Sebski123/p-ktane/Design/Photos/20190628_165110.jpg

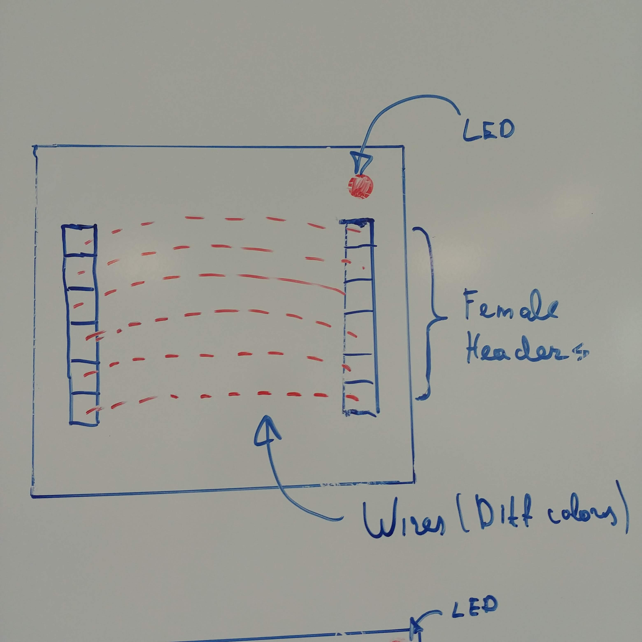
Design/Photos/20190628_165110.jpg
