Sebski123/p-ktane/Design/Photos/20190628_165116.jpg

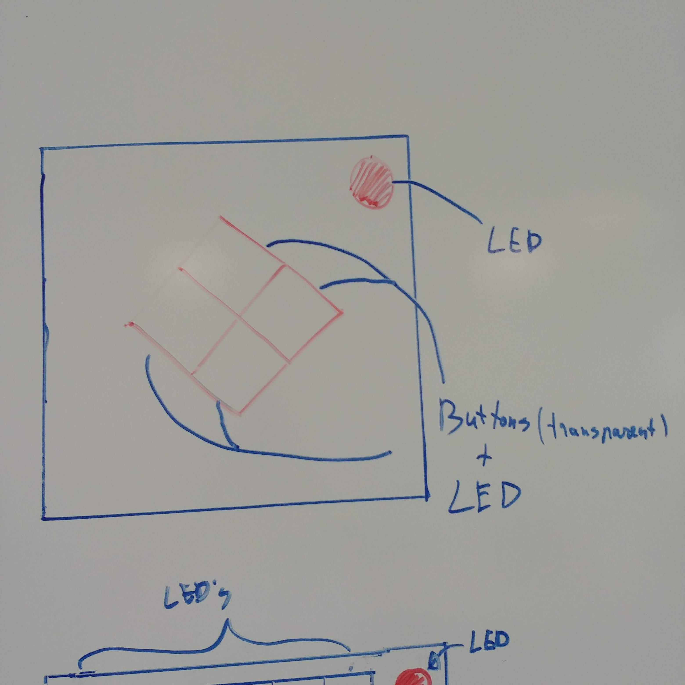
Design/Photos/20190628_165116.jpg
