Sebski123/p-ktane/Design/Photos/20190628_165210.jpg

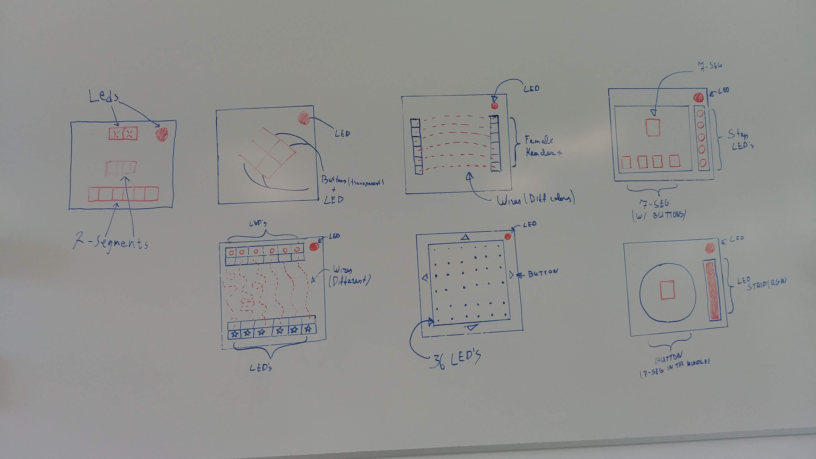
Design/Photos/20190628_165210.jpg
