Sebski123/p-ktane/Modules/buttonModule/MXFrameBottom.SLDPRT

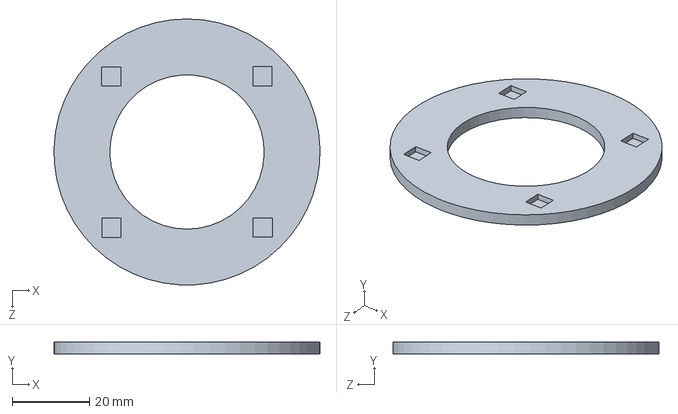
[picture p24: CAD file, 2020-05-21]
Modules/buttonModule/MXFrameBottom.SLDPRT
69.0 x 3.00 x 69.0 mm
