Sebski123/p-ktane/Modules/mazeModule/Maze face plate.SLDPRT

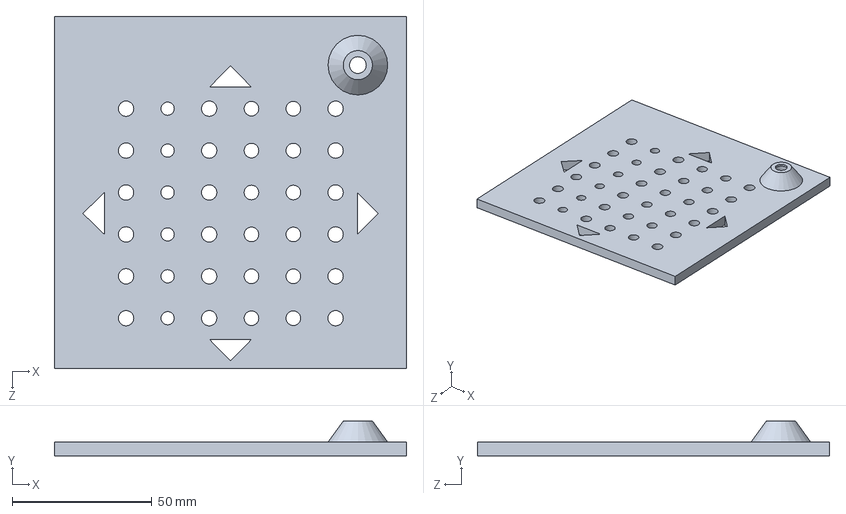
[picture p25: CAD file, 2020-05-14]
Modules/mazeModule/Maze face plate.SLDPRT
126.0 x 12.5 x 126.0 mm
