Sebski123/p-ktane/Modules/memoryModule/TRIANGLE.SLDPRT

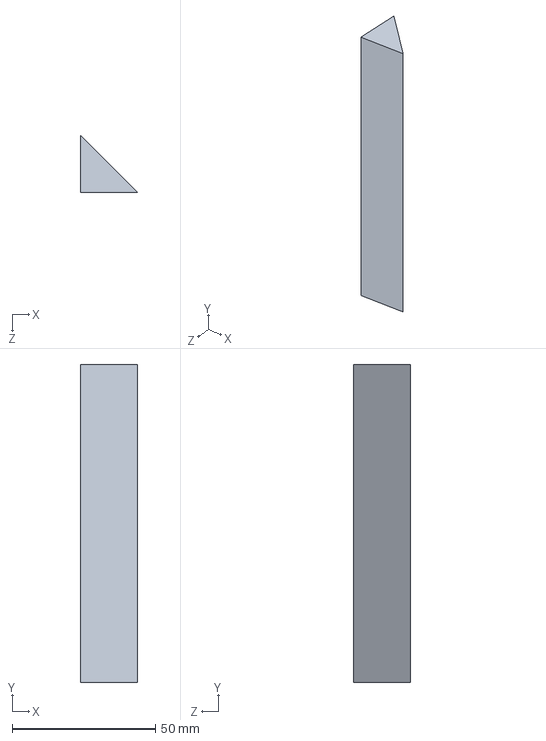
[picture p26: CAD file, 2020-05-26]
Modules/memoryModule/TRIANGLE.SLDPRT
20.0 x 111.0 x 20.0 mm
