Sebski123/p-ktane/Modules/simonSaysModule/front_plate_simon.stp

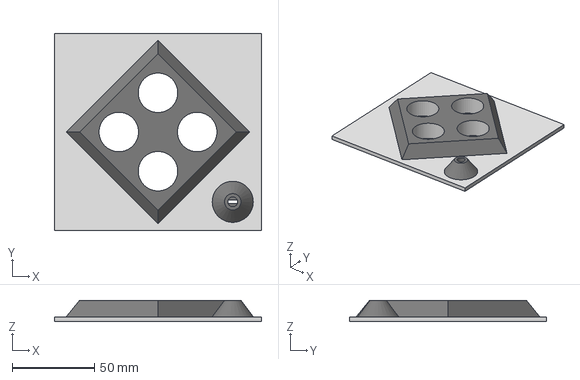
[picture p27: CAD file, 2020-04-02]
Modules/simonSaysModule/front_plate_simon.stp
126.0 x 120.0 x 13.0 mm
