Sebski123/p-ktane/Design/Box/Box parts/BoxTop.SLDPRT

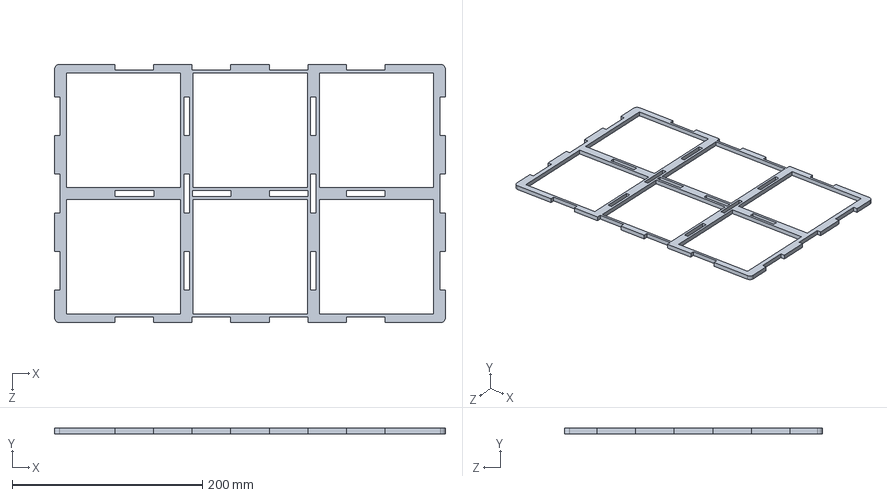
[picture p28: CAD file, 2020-04-29]
Design/Box/Box parts/BoxTop.SLDPRT
410.7 x 6.00 x 271.4 mm
