Sebski123/p-ktane/Design/Box/DXF FILES/SidesSmall.dxf

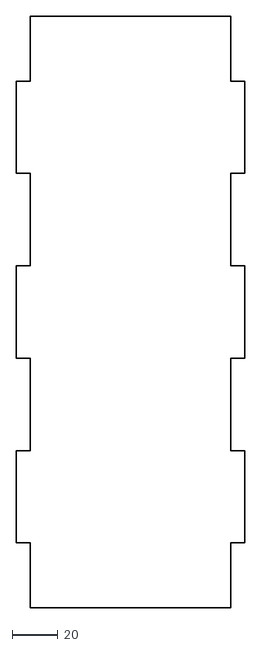
[picture p29: CAD file, 2020-04-29]
Design/Box/DXF FILES/SidesSmall.dxf
100.0 x 259.4
