Sebski123/p-ktane/Modules/buttonModule/MXFrameTop.SLDPRT

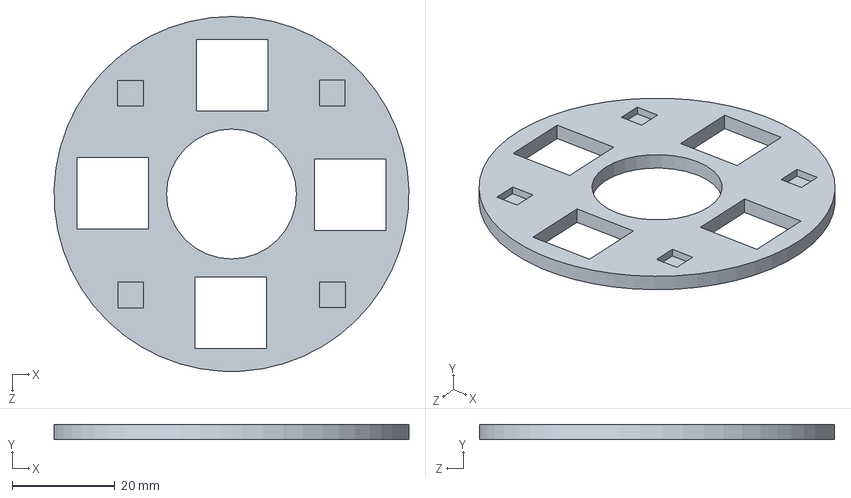
[picture p30: CAD file, 2020-05-21]
Modules/buttonModule/MXFrameTop.SLDPRT
69.0 x 3.00 x 69.0 mm
