Sebski123/p-ktane/Design/Box/Box parts/BoxBottom.SLDPRT

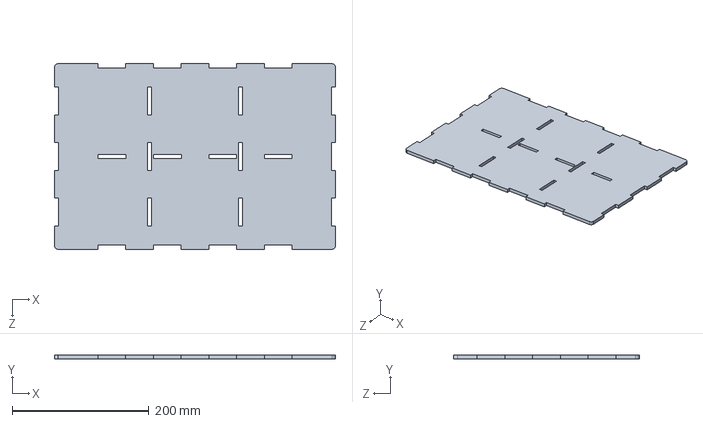
[picture p31: CAD file, 2020-04-29]
Design/Box/Box parts/BoxBottom.SLDPRT
410.7 x 6.00 x 271.4 mm
