Sebski123/p-ktane/Design/Box/DXF FILES/BoxBottom.dxf

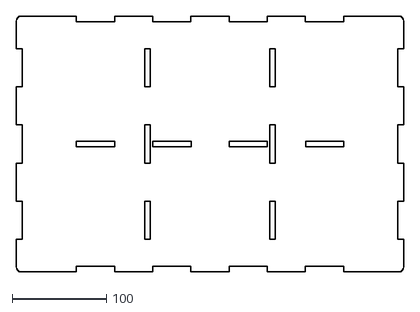
[picture p32: CAD file, 2020-04-29]
Design/Box/DXF FILES/BoxBottom.dxf
410.7 x 271.4
