Sebski123/p-ktane/Modules/buttonModule/Button base.SLDPRT

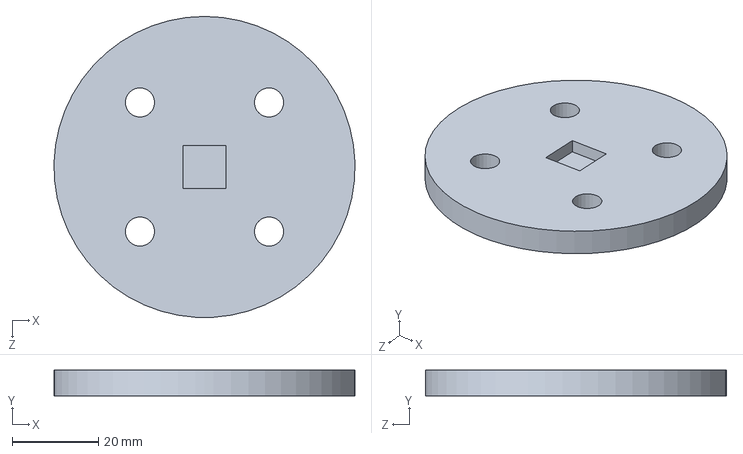
[picture p33: CAD file, 2020-05-21]
Modules/buttonModule/Button base.SLDPRT
70.0 x 6.00 x 70.0 mm
