Sebski123/p-ktane/Modules/memoryModule/Memory button base.SLDPRT

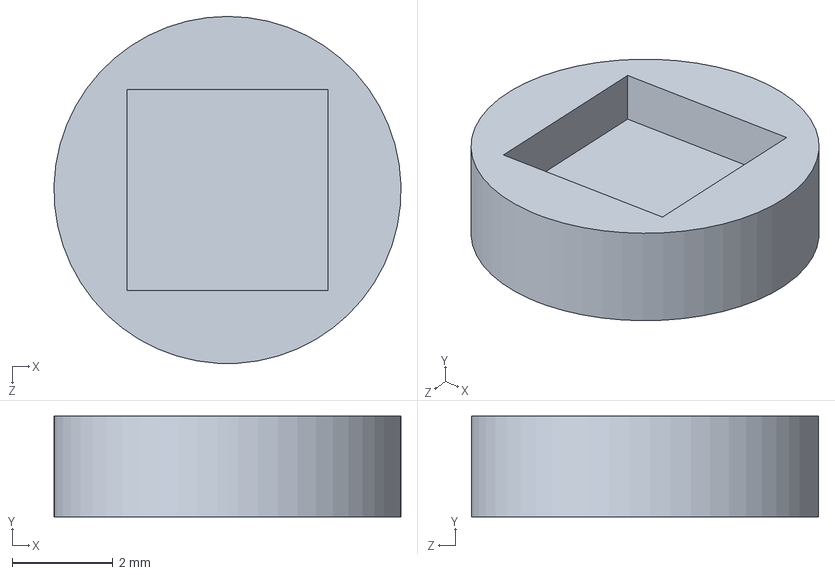
[picture p34: CAD file, 2020-04-14]
Modules/memoryModule/Memory button base.SLDPRT
6.90 x 2.00 x 6.90 mm
