Sebski123/p-ktane/Design/Box/Box parts/InsideLarge.SLDPRT

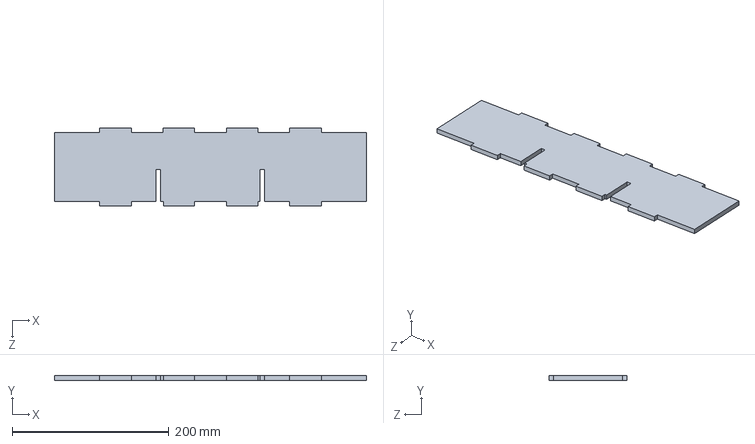
[picture p35: CAD file, 2020-04-29]
Design/Box/Box parts/InsideLarge.SLDPRT
398.7 x 6.00 x 100.0 mm
