Sebski123/p-ktane/Design/Box/DXF FILES/SidesLarge.dxf

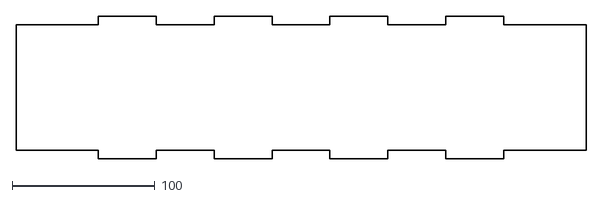
[picture p36: CAD file, 2020-04-29]
Design/Box/DXF FILES/SidesLarge.dxf
398.8 x 100.0
