Sebski123/p-ktane/Modules/buttonModule/MXSwitchLegs.SLDPRT

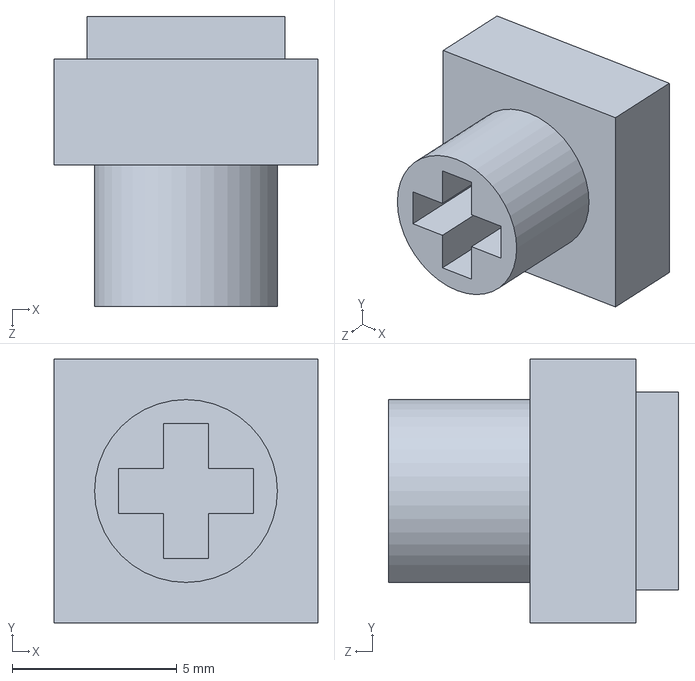
[picture p37: CAD file, 2020-05-21]
Modules/buttonModule/MXSwitchLegs.SLDPRT
8.00 x 8.00 x 8.80 mm
