Sebski123/p-ktane/Modules/memoryModule/front_plate_memory.stp

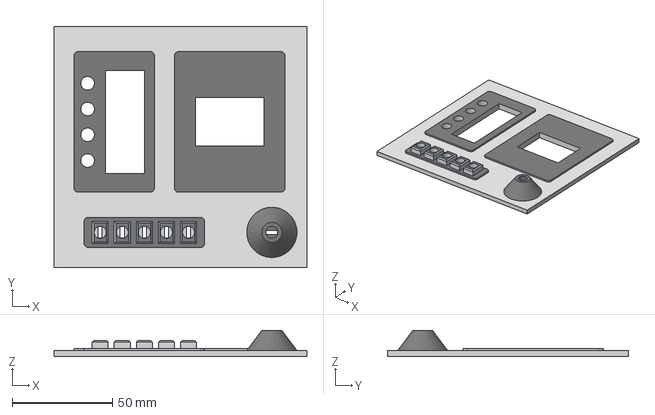
[picture p38: CAD file, 2020-04-02]
Modules/memoryModule/front_plate_memory.stp
126.0 x 120.0 x 13.0 mm
