Sebski123/p-ktane/Design/Box/DXF FILES/InsideSmall.dxf

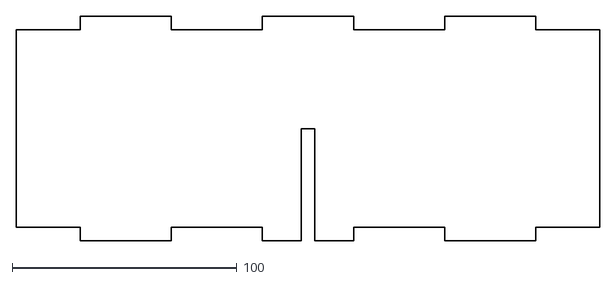
[picture p39: CAD file, 2020-04-29]
Design/Box/DXF FILES/InsideSmall.dxf
259.4 x 100.0
