Sebski123/p-ktane/Modules/buttonModule/Button face plate side bar.SLDPRT

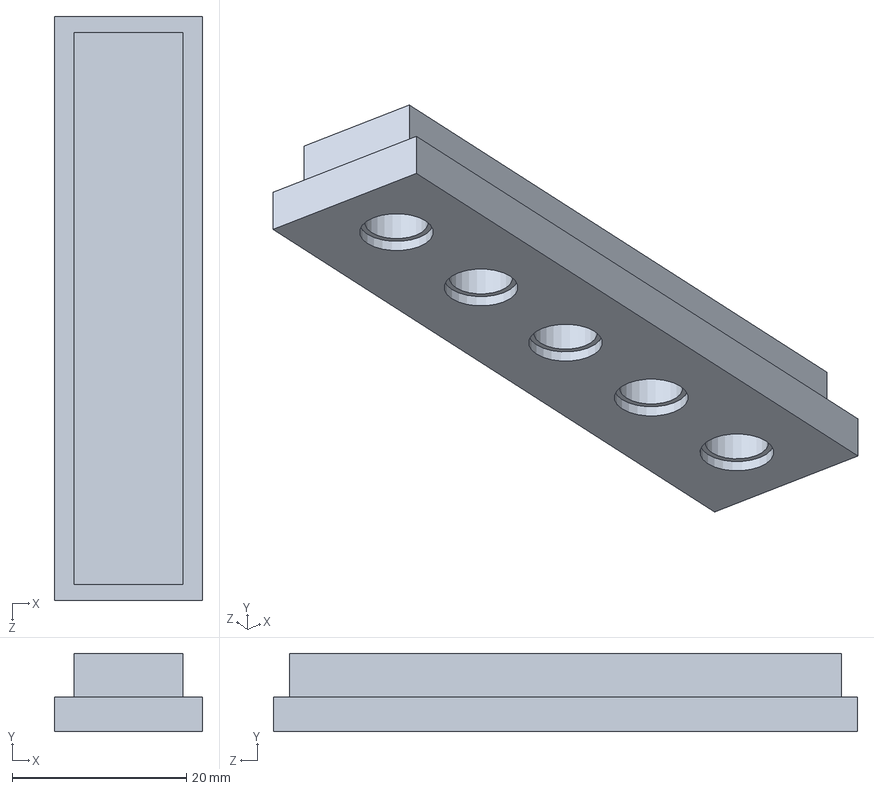
[picture p40: CAD file, 2020-05-05]
Modules/buttonModule/Button face plate side bar.SLDPRT
17.0 x 9.00 x 67.0 mm
