Sebski123/p-ktane/Modules/buttonModule/Button face plate.SLDPRT

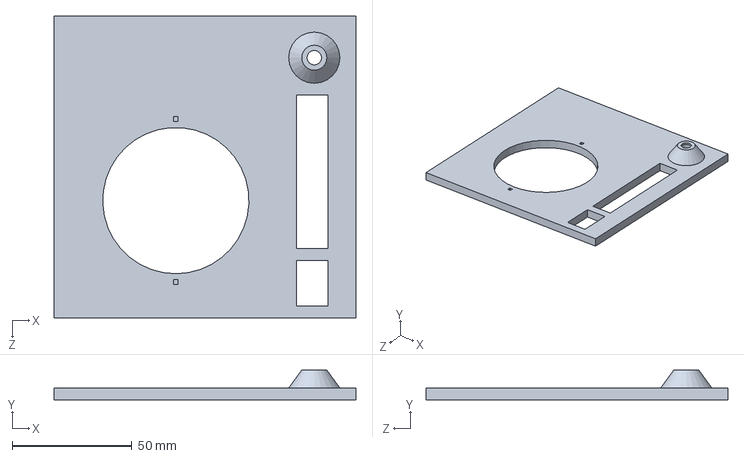
[picture p41: CAD file, 2020-04-22]
Modules/buttonModule/Button face plate.SLDPRT
126.0 x 12.5 x 126.0 mm
