Sebski123/p-ktane/Modules/buttonModule/Button middle.SLDPRT

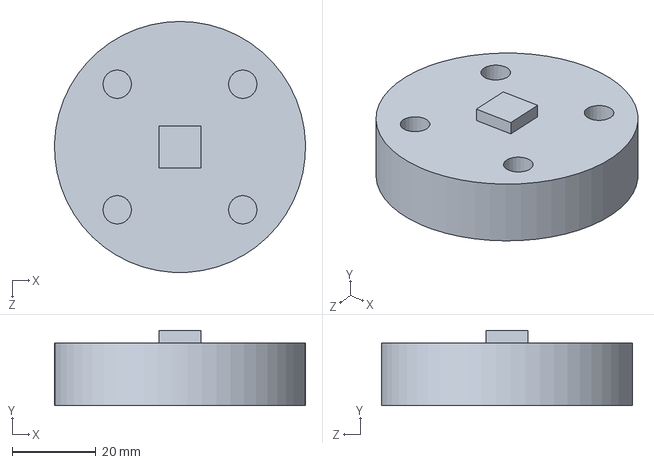
[picture p42: CAD file, 2020-04-22]
Modules/buttonModule/Button middle.SLDPRT
60.0 x 18.0 x 60.0 mm
