Sebski123/p-ktane/Modules/buttonModule/Button face plate ring.SLDPRT

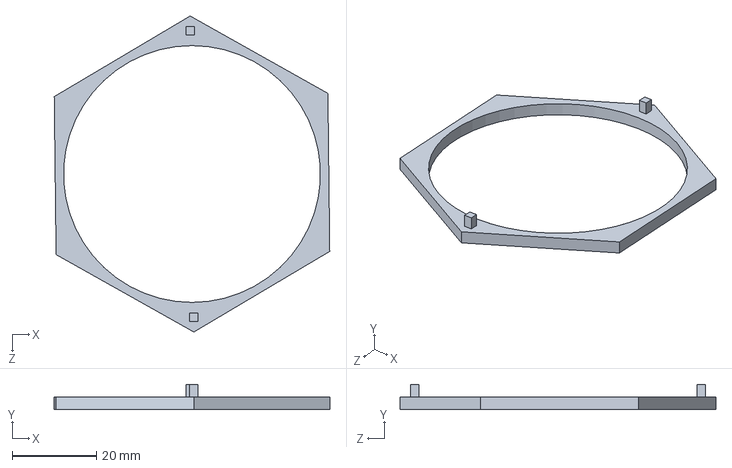
[picture p43: CAD file, 2020-04-14]
Modules/buttonModule/Button face plate ring.SLDPRT
65.4 x 6.00 x 75.1 mm
