Sebski123/p-ktane/Modules/buttonModule/Button top.SLDPRT

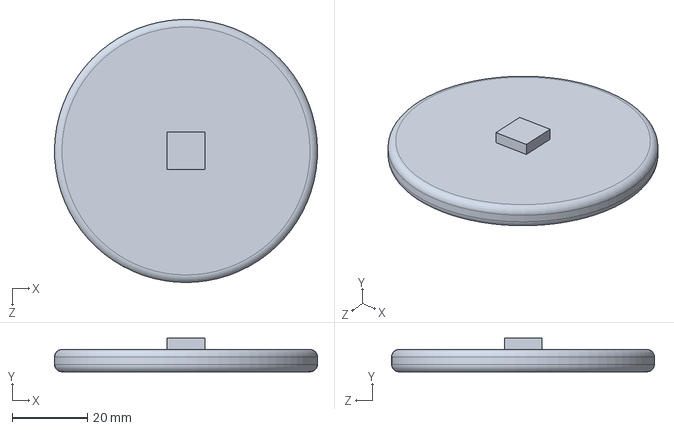
[picture p44: CAD file, 2020-04-10]
Modules/buttonModule/Button top.SLDPRT
70.0 x 9.00 x 70.0 mm
