Sebski123/p-ktane/Design/Schematics/allModules.sch

## EAGLE design Design/Schematics/allModules.sch (2020-06-12)

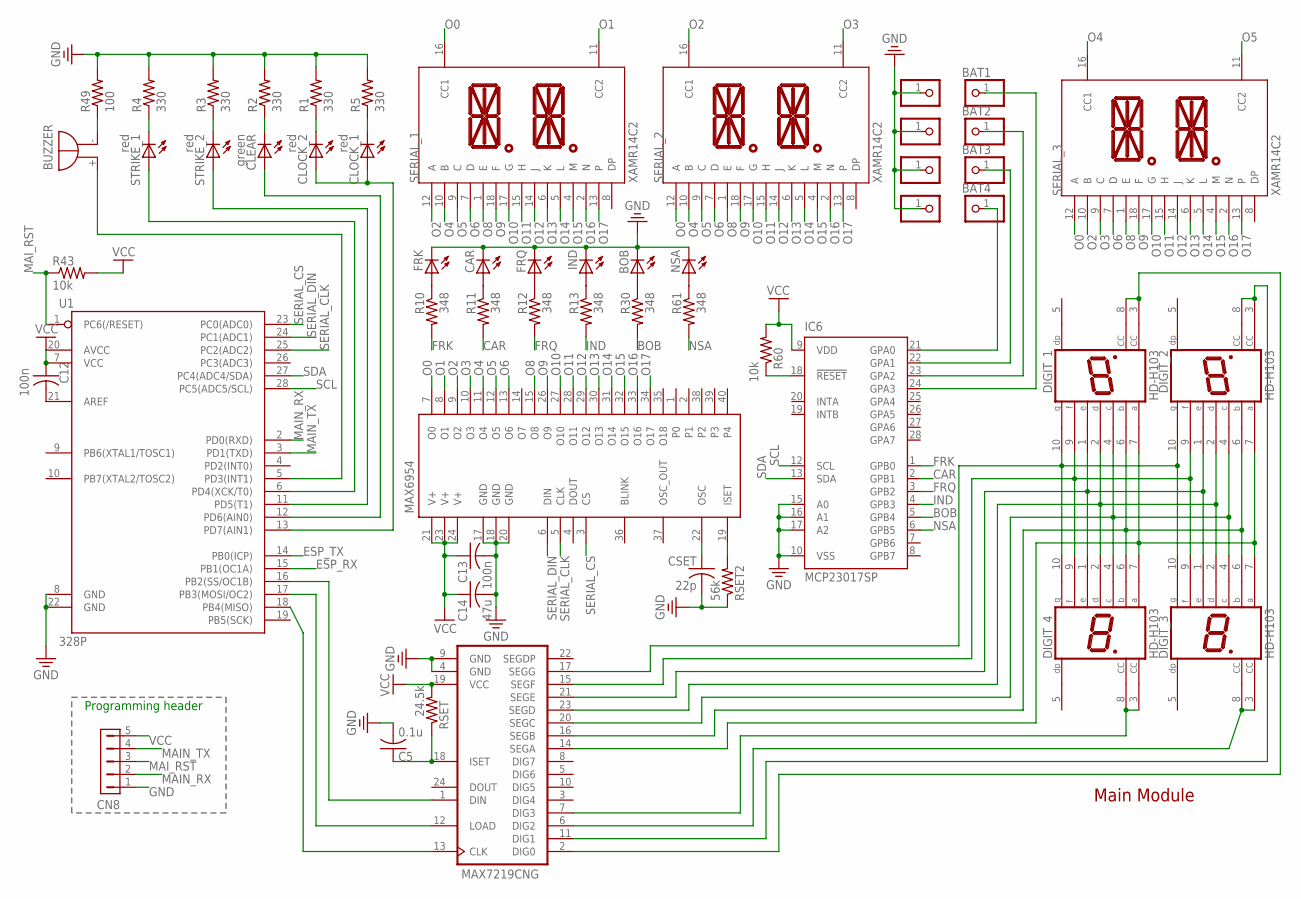
[picture p52: schematic allModules.sch, sheet 1]

Parts:
BAT1, BAT2, BAT3, BAT4: PINHD-1X1; 1X01
BOB: LED5MM
BUZZER: EB2209A
C5: 0.1u; C025-024X044
C12, C13: 100n; C025-024X044
C14: 47u; C025-024X044
CAR: LED5MM
CLEAR: green; LED5MM
CLOCK_1, CLOCK_2: red; LED5MM
CN8: HDR-1X5-SIP-100; SIP-100-5V
CSET: 22p; C025-024X044
DIGIT_1, DIGIT_2, DIGIT_3, DIGIT_4: HD-H103; HDSP-M
FRK: LED5MM
FRQ: LED5MM
IC1: MAX7219CNG; DIL24-3
IC6: MCP23017SP; DIL28-3
IND: LED5MM
JP17, JP18, JP19, JP20: PINHD-1X1; 1X01
MAX6954: MAX6954
NSA: LED5MM
R1, R2, R3, R4, R5: 330; 0309/12
R10, R11, R12, R13, R30, R61: 348; 0204/7
R43: 10k; 0309/12
R49: 100; 0309/12
R60: 10k; 0204/7
RSET: 24.5k; 0204/7
RSET2: 56k; 0204/7
SERIAL_1, SERIAL_2, SERIAL_3: XAMR14C2
STRIKE_1, STRIKE_2: red; LED5MM
U1: 328P; DIP28

Connections:
BAT1: BAT1.1, IC6.24 (GPA3)
BOB: IC6.5 (GPB4), R30.2
CAR: IC6.2 (GPB1), R11.2
ESP_RX: U1.15 (PB1(OC1A))
ESP_TX: U1.14 (PB0(ICP))
FRK: IC6.1 (GPB0), R10.2
FRQ: IC6.3 (GPB2), R12.2
GND: BOB.K (C), C5.2, C13.2, C14.2, CAR.K (C), CN8.1, CSET.2, FRK.K (C), FRQ.K (C), IC1.4 (GND), IC1.9 (GND), IC6.10 (VSS), IC6.15 (A0), IC6.16 (A1), IC6.17 (A2), IND.K (C), JP17.1, JP18.1, JP19.1, JP20.1, MAX6954.17 (GND), MAX6954.18 (GND), MAX6954.20 (GND), NSA.K (C), R1.2, R2.2, R3.2, R4.2, R5.2, R49.2, RSET2.1, U1.8 (GND), U1.22 (GND)
IND: IC6.4 (GPB3), R13.2
MAIN_RX: CN8.2, U1.2 (PD0(RXD))
MAIN_TX: CN8.4, U1.3 (PD1(TXD))
MAI_RST: CN8.3, R43.1, U1.1 (PC6(/RESET))
unnamed: DIGIT_1.7 (A), DIGIT_2.7 (A), DIGIT_3.7 (A), DIGIT_4.7 (A), IC1.14 (SEGA)
unnamed: DIGIT_1.6 (B), DIGIT_2.6 (B), DIGIT_3.6 (B), DIGIT_4.6 (B), IC1.16 (SEGB)
unnamed: DIGIT_1.4 (C), DIGIT_2.4 (C), DIGIT_3.4 (C), DIGIT_4.4 (C), IC1.20 (SEGC)
unnamed: DIGIT_1.2 (D), DIGIT_2.2 (D), DIGIT_3.2 (D), DIGIT_4.2 (D), IC1.23 (SEGD)
unnamed: DIGIT_1.1 (E), DIGIT_2.1 (E), DIGIT_3.1 (E), DIGIT_4.1 (E), IC1.21 (SEGE)
unnamed: DIGIT_1.9 (F), DIGIT_2.9 (F), DIGIT_3.9 (F), DIGIT_4.9 (F), IC1.15 (SEGF)
unnamed: DIGIT_1.10 (G), DIGIT_2.10 (G), DIGIT_3.10 (G), DIGIT_4.10 (G), IC1.17 (SEGG)
unnamed: CSET.1, MAX6954.22 (OSC)
unnamed: MAX6954.19 (ISET), RSET2.2
unnamed: IC1.12 (LOAD), U1.17 (PB3(MOSI/OC2))
unnamed: IC1.1 (DIN), U1.16 (PB2(SS/OC1B))
unnamed: IC1.13 (CLK), U1.18 (PB4(MISO))
unnamed: DIGIT_2.3 (CC), DIGIT_2.8 (CC), IC1.11 (DIG1)
unnamed: DIGIT_1.3 (CC), DIGIT_1.8 (CC), IC1.2 (DIG0)
unnamed: BUZZER.-, R49.1
unnamed: DIGIT_3.3 (CC), DIGIT_3.8 (CC), IC1.6 (DIG2)
unnamed: DIGIT_4.3 (CC), DIGIT_4.8 (CC), IC1.7 (DIG3)
unnamed: R4.1, STRIKE_1.K (C)
unnamed: R3.1, STRIKE_2.K (C)
unnamed: CLEAR.K (C), R2.1
unnamed: CLOCK_2.K (C), R1.1
unnamed: CLOCK_1.K (C), R5.1
unnamed: STRIKE_1.A, U1.6 (PD4(XCK/T0))
unnamed: STRIKE_2.A, U1.11 (PD5(T1))
unnamed: CLEAR.A, U1.12 (PD6(AIN0))
unnamed: CLOCK_1.A, CLOCK_2.A, U1.13 (PD7(AIN1))
unnamed: C5.1, IC1.18 (ISET), RSET.1
unnamed: IC6.18 (!RESET), R60.1
unnamed: BUZZER.+, U1.5 (PD3(INT1))
unnamed: FRK.A, R10.1
unnamed: BAT2.1, IC6.23 (GPA2)
unnamed: C12.2, U1.21 (AREF)
unnamed: BAT3.1, IC6.22 (GPA1)
unnamed: BAT4.1, IC6.21 (GPA0)
unnamed: CAR.A, R11.1
unnamed: FRQ.A, R12.1
unnamed: IND.A, R13.1
unnamed: BOB.A, R30.1
unnamed: NSA.A, R61.1
NSA: IC6.6 (GPB5), R61.2
O0: MAX6954.7 (O0), SERIAL_1.16 (CC1), SERIAL_2.12 (A), SERIAL_3.12 (A)
O1: MAX6954.8 (O1), SERIAL_1.11 (CC2)
O2: MAX6954.9 (O2), SERIAL_1.12 (A), SERIAL_2.16 (CC1), SERIAL_3.10 (B)
O3: MAX6954.10 (O3), SERIAL_2.11 (CC2), SERIAL_3.9 (C)
O4: MAX6954.11 (O4), SERIAL_1.10 (B), SERIAL_2.10 (B), SERIAL_3.16 (CC1)
O5: MAX6954.12 (O5), SERIAL_1.9 (C), SERIAL_2.9 (C), SERIAL_3.11 (CC2)
O6: MAX6954.13 (O6), SERIAL_1.7 (D), SERIAL_2.7 (D), SERIAL_3.7 (D)
O8: MAX6954.15 (O8), SERIAL_1.1 (E), SERIAL_2.1 (E), SERIAL_3.1 (E)
O9: MAX6954.26 (O9), SERIAL_1.18 (F), SERIAL_2.18 (F), SERIAL_3.18 (F)
O10: MAX6954.27 (O10), SERIAL_1.17 (G), SERIAL_2.17 (G), SERIAL_3.17 (G)
O11: MAX6954.28 (O11), SERIAL_1.15 (H), SERIAL_2.15 (H), SERIAL_3.15 (H)
O12: MAX6954.29 (O12), SERIAL_1.14 (J), SERIAL_2.14 (J), SERIAL_3.14 (J)
O13: MAX6954.30 (O13), SERIAL_1.6 (K), SERIAL_2.6 (K), SERIAL_3.6 (K)
O14: MAX6954.31 (O14), SERIAL_1.5 (L), SERIAL_2.5 (L), SERIAL_3.5 (L)
O15: MAX6954.32 (O15), SERIAL_1.4 (M), SERIAL_2.4 (M), SERIAL_3.4 (M)
O16: MAX6954.33 (O16), SERIAL_1.2 (N), SERIAL_2.2 (N), SERIAL_3.2 (N)
O17: MAX6954.34 (O17), SERIAL_1.13, SERIAL_2.13, SERIAL_3.13
SCL: IC6.12 (SCL), U1.28 (PC5(ADC5/SCL))
SDA: IC6.13 (SDA), U1.27 (PC4(ADC4/SDA))
SERIAL_CLK: MAX6954.5 (CLK), U1.25 (PC2(ADC2))
SERIAL_CS: MAX6954.3 (CS), U1.23 (PC0(ADC0))
SERIAL_DIN: MAX6954.6 (DIN), U1.24 (PC1(ADC1))
VCC: C12.1, C13.1, C14.1, CN8.5, IC1.19 (VCC), IC6.9 (VDD), MAX6954.21 (V+), MAX6954.23 (V+), MAX6954.24 (V+), R43.2, R60.2, RSET.2, U1.7 (VCC), U1.20 (AVCC)

Notes on the sheet:
Main Module
Programming header

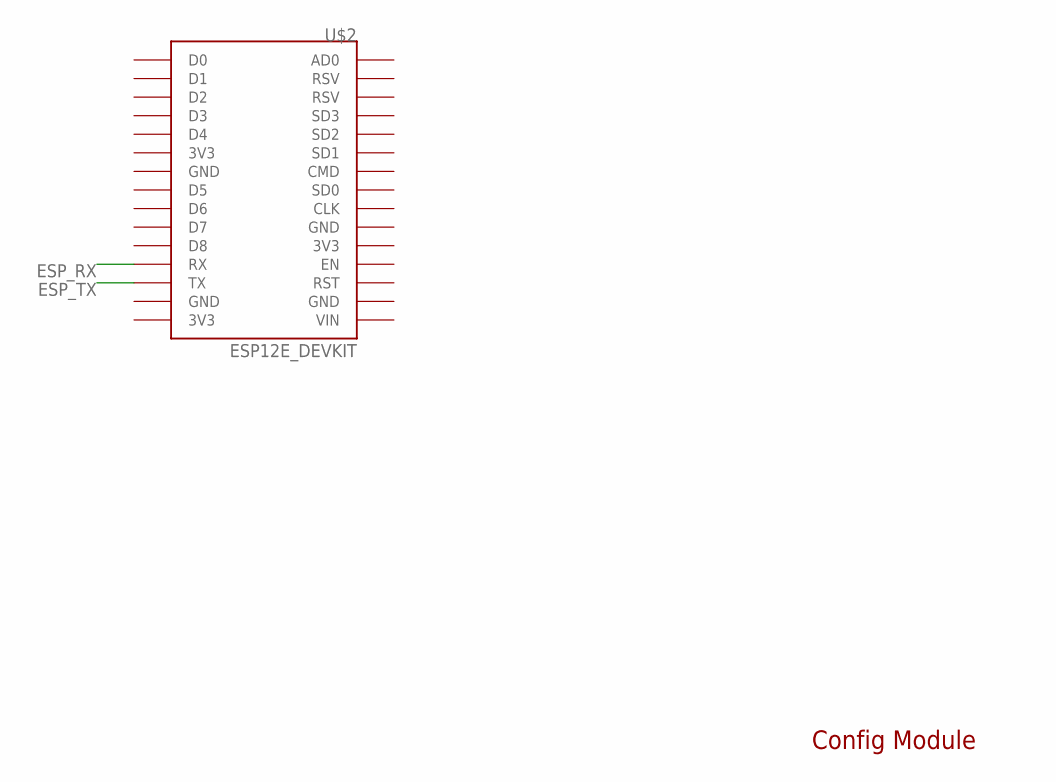
[picture p53: schematic allModules.sch, sheet 2]

Parts:
U$2: ESP12E_DEVKIT

Connections:
ESP_RX: U$2.RX
ESP_TX: U$2.TX

Notes on the sheet:
Config Module

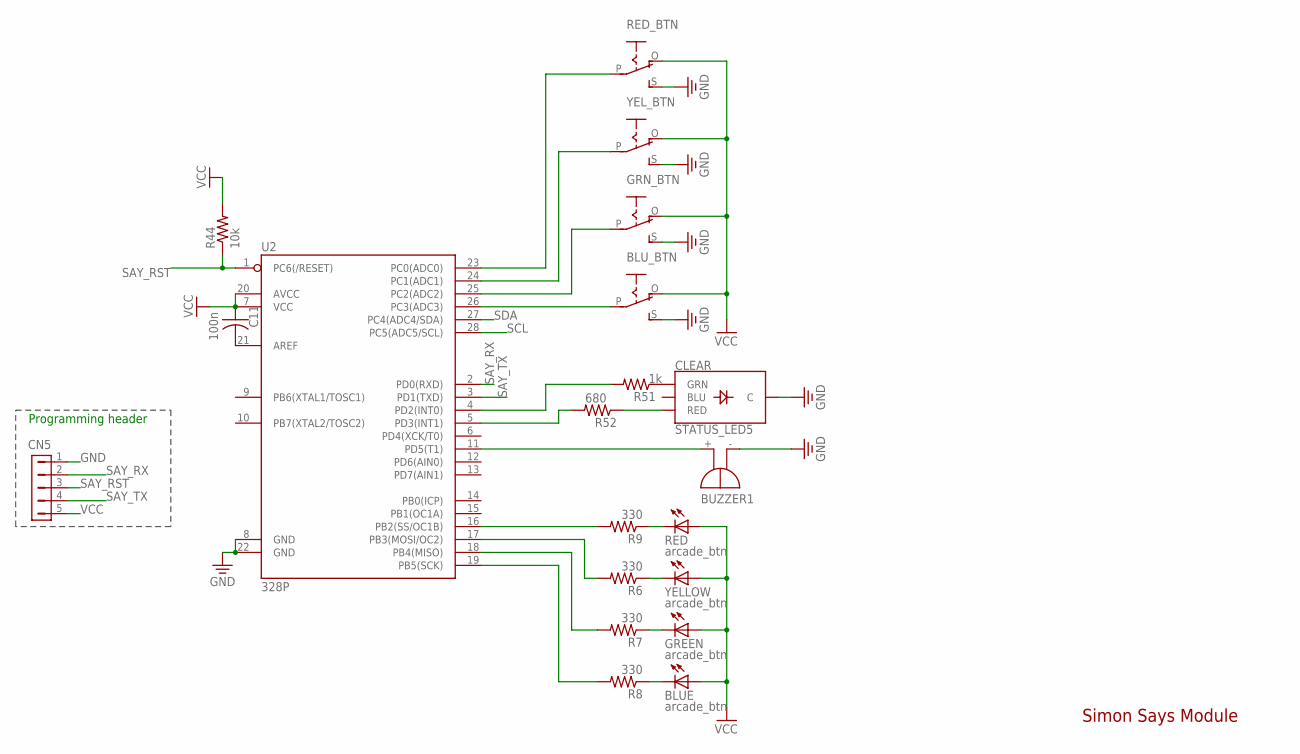
[picture p54: schematic allModules.sch, sheet 3]

Parts:
BLUE: arcade_btn; LED5MM
BLU_BTN: EG1218S; EG1218
BUZZER1: EB2209A
C11: 100n; C025-024X044
CN5: HDR-1X5-SIP-100; SIP-100-5V
GREEN: arcade_btn; LED5MM
GRN_BTN: EG1218S; EG1218
R6, R7, R8, R9: 330; 0309/12
R44: 10k; 0309/12
R51: 1k; 0805-THM
R52: 680; 0805-THM
RED: arcade_btn; LED5MM
RED_BTN: EG1218S; EG1218
STATUS_LED5: CLEAR; LED-RGB-THRU
U2: 328P; DIP28
YELLOW: arcade_btn; LED5MM
YEL_BTN: EG1218S; EG1218

Connections:
GND: BLU_BTN.S, BUZZER1.-, CN5.1, GRN_BTN.S, RED_BTN.S, STATUS_LED5.2 (C), U2.8 (GND), U2.22 (GND), YEL_BTN.S
unnamed: BUZZER1.+, U2.11 (PD5(T1))
unnamed: BLU_BTN.P, U2.26 (PC3(ADC3))
unnamed: GRN_BTN.P, U2.25 (PC2(ADC2))
unnamed: U2.24 (PC1(ADC1)), YEL_BTN.P
unnamed: RED_BTN.P, U2.23 (PC0(ADC0))
unnamed: R6.2, U2.17 (PB3(MOSI/OC2))
unnamed: BLUE.K (C), R8.1
unnamed: GREEN.K (C), R7.1
unnamed: R6.1, YELLOW.K (C)
unnamed: R9.1, RED.K (C)
unnamed: R7.2, R8.2, U2.18 (PB4(MISO)), U2.19 (PB5(SCK))
unnamed: R52.2, U2.5 (PD3(INT1))
unnamed: R51.2, U2.4 (PD2(INT0))
unnamed: R9.2, U2.16 (PB2(SS/OC1B))
unnamed: C11.2, U2.21 (AREF)
unnamed: R51.1, STATUS_LED5.3 (GRN)
unnamed: R52.1, STATUS_LED5.1 (RED)
SAY_RST: CN5.3, R44.1, U2.1 (PC6(/RESET))
SAY_RX: CN5.2, U2.2 (PD0(RXD))
SAY_TX: CN5.4, U2.3 (PD1(TXD))
SCL: U2.28 (PC5(ADC5/SCL))
SDA: U2.27 (PC4(ADC4/SDA))
VCC: BLUE.A, BLU_BTN.O, C11.1, CN5.5, GREEN.A, GRN_BTN.O, R44.2, RED.A, RED_BTN.O, U2.7 (VCC), U2.20 (AVCC), YELLOW.A, YEL_BTN.O

Notes on the sheet:
Simon Says Module
Programming header

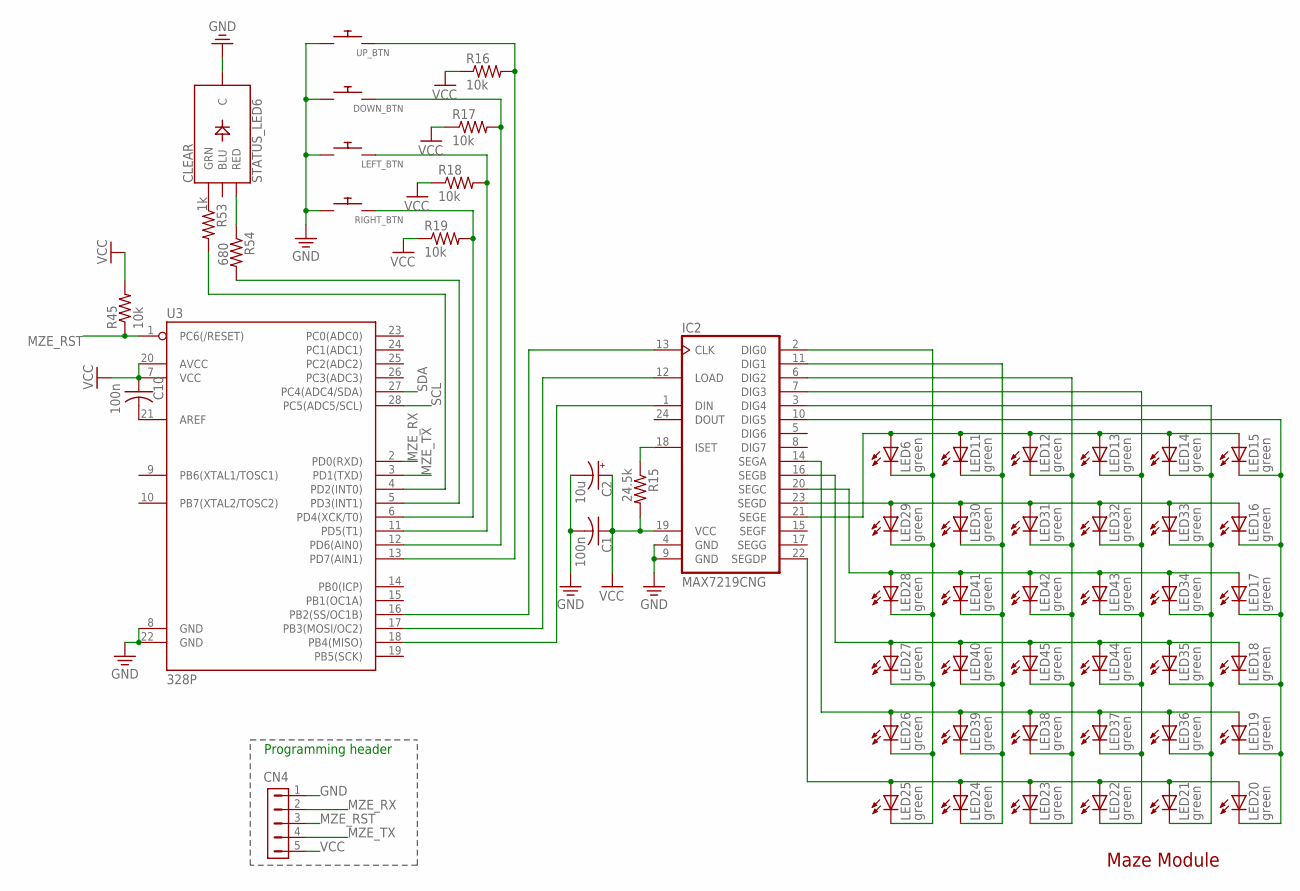
[picture p55: schematic allModules.sch, sheet 4]

Parts:
C1, C10: 100n; C025-024X044
C2: 10u; 085CS_1AR
CN4: HDR-1X5-SIP-100; SIP-100-5V
DOWN_BTN: SWITCH_PUSHBUTTONEVQ-PE; TACT_PANA-EVQ
IC2: MAX7219CNG; DIL24-3
LED6, LED11, LED12, LED13, LED14, LED15, LED16, LED17, LED18, LED19, LED20, LED21, LED22, LED23, LED24, LED25, LED26, LED27, LED28, LED29, LED30, LED31, LED32, LED33, LED34, LED35, LED36, LED37, LED38, LED39, LED40, LED41, LED42, LED43, LED44, LED45: green; LED5MM
LEFT_BTN: SWITCH_PUSHBUTTONEVQ-PE; TACT_PANA-EVQ
R15: 24.5k; 0309/12
R16, R17, R18, R19, R45: 10k; 0309/12
R53: 1k; 0805-THM
R54: 680; 0805-THM
RIGHT_BTN: SWITCH_PUSHBUTTONEVQ-PE; TACT_PANA-EVQ
STATUS_LED6: CLEAR; LED-RGB-THRU
U3: 328P; DIP28
UP_BTN: SWITCH_PUSHBUTTONEVQ-PE; TACT_PANA-EVQ

Connections:
GND: C1.2, C2.-, CN4.1, DOWN_BTN.P$1, IC2.4 (GND), IC2.9 (GND), LEFT_BTN.P$1, RIGHT_BTN.P$1, STATUS_LED6.2 (C), U3.8 (GND), U3.22 (GND), UP_BTN.P$1
MZE_RST: CN4.3, R45.1, U3.1 (PC6(/RESET))
MZE_RX: CN4.2, U3.2 (PD0(RXD))
MZE_TX: CN4.4, U3.3 (PD1(TXD))
unnamed: IC2.22 (SEGDP), LED20.A, LED21.A, LED22.A, LED23.A, LED24.A, LED25.A
unnamed: IC2.14 (SEGA), LED19.A, LED26.A, LED36.A, LED37.A, LED38.A, LED39.A
unnamed: IC2.16 (SEGB), LED18.A, LED27.A, LED35.A, LED40.A, LED44.A, LED45.A
unnamed: IC2.20 (SEGC), LED17.A, LED28.A, LED34.A, LED41.A, LED42.A, LED43.A
unnamed: IC2.2 (DIG0), LED6.K (C), LED25.K (C), LED26.K (C), LED27.K (C), LED28.K (C), LED29.K (C)
unnamed: IC2.21 (SEGE), LED11.A, LED12.A, LED13.A, LED14.A, LED15.A
unnamed: IC2.23 (SEGD), LED16.A, LED29.A, LED30.A, LED31.A, LED32.A, LED33.A
unnamed: R16.2, U3.13 (PD7(AIN1)), UP_BTN.P$2
unnamed: IC2.11 (DIG1), LED11.K (C), LED24.K (C), LED30.K (C), LED39.K (C), LED40.K (C), LED41.K (C)
unnamed: IC2.6 (DIG2), LED12.K (C), LED23.K (C), LED31.K (C), LED38.K (C), LED42.K (C), LED45.K (C)
unnamed: IC2.7 (DIG3), LED13.K (C), LED22.K (C), LED32.K (C), LED37.K (C), LED43.K (C), LED44.K (C)
unnamed: IC2.3 (DIG4), LED14.K (C), LED21.K (C), LED33.K (C), LED34.K (C), LED35.K (C), LED36.K (C)
unnamed: IC2.10 (DIG5), LED15.K (C), LED16.K (C), LED17.K (C), LED18.K (C), LED19.K (C), LED20.K (C)
unnamed: DOWN_BTN.P$2, R17.2, U3.12 (PD6(AIN0))
unnamed: LEFT_BTN.P$2, R18.2, U3.11 (PD5(T1))
unnamed: IC2.18 (ISET), R15.1
unnamed: R19.2, RIGHT_BTN.P$2, U3.6 (PD4(XCK/T0))
unnamed: IC2.1 (DIN), U3.18 (PB4(MISO))
unnamed: IC2.13 (CLK), U3.16 (PB2(SS/OC1B))
unnamed: IC2.12 (LOAD), U3.17 (PB3(MOSI/OC2))
unnamed: R54.2, U3.5 (PD3(INT1))
unnamed: R53.2, U3.4 (PD2(INT0))
unnamed: C10.2, U3.21 (AREF)
unnamed: R53.1, STATUS_LED6.3 (GRN)
unnamed: R54.1, STATUS_LED6.1 (RED)
SCL: U3.28 (PC5(ADC5/SCL))
SDA: U3.27 (PC4(ADC4/SDA))
VCC: C1.1, C2.+, C10.1, CN4.5, IC2.19 (VCC), R15.2, R16.1, R17.1, R18.1, R19.1, R45.2, U3.7 (VCC), U3.20 (AVCC)
VCC2: LED6.A

Notes on the sheet:
Maze Module
Programming header

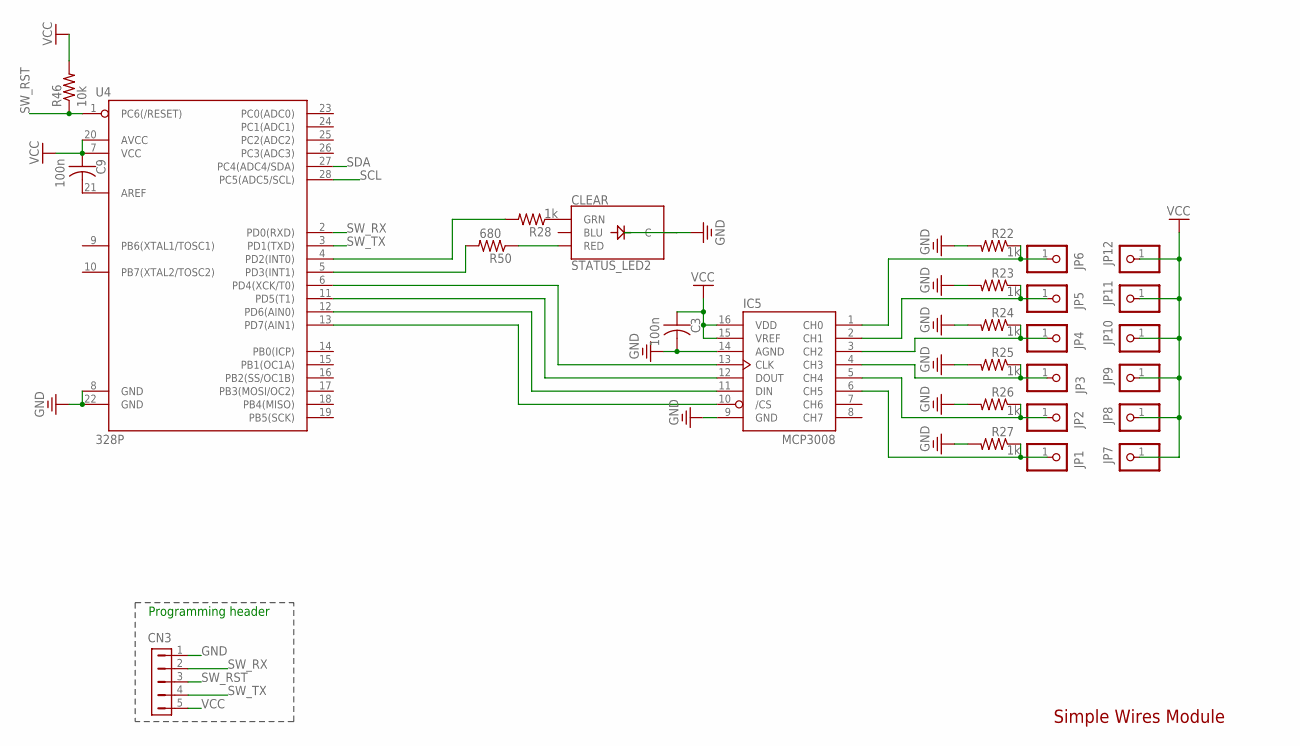
[picture p56: schematic allModules.sch, sheet 5]

Parts:
C3, C9: 100n; C025-024X044
CN3: HDR-1X5-SIP-100; SIP-100-5V
IC5: MCP3008; DIL16
JP1, JP2, JP3, JP4, JP5, JP6, JP7, JP8, JP9, JP10, JP11, JP12: PINHD-1X1; 1X01
R22, R23, R24, R25, R26, R27, R28: 1k; 0805-THM
R46: 10k; 0309/12
R50: 680; 0805-THM
STATUS_LED2: CLEAR; LED-RGB-THRU
U4: 328P; DIP28

Connections:
GND: C3.2, CN3.1, IC5.9 (GND), IC5.14 (AGND), R22.2, R23.2, R24.2, R25.2, R26.2, R27.2, U4.8 (GND), U4.22 (GND)
unnamed: R28.1, STATUS_LED2.3 (GRN)
unnamed: IC5.1 (CH0), JP6.1, R22.1
unnamed: IC5.6 (CH5), JP1.1, R27.1
unnamed: R50.1, STATUS_LED2.1 (RED)
unnamed: IC5.5 (CH4), JP2.1, R26.1
unnamed: IC5.4 (CH3), JP3.1, R25.1
unnamed: IC5.3 (CH2), JP4.1, R24.1
unnamed: IC5.2 (CH1), JP5.1, R23.1
unnamed: R28.2, U4.4 (PD2(INT0))
unnamed: R50.2, U4.5 (PD3(INT1))
unnamed: IC5.13 (CLK), U4.6 (PD4(XCK/T0))
unnamed: IC5.12 (DOUT), U4.11 (PD5(T1))
unnamed: IC5.11 (DIN), U4.12 (PD6(AIN0))
unnamed: IC5.10 (/CS), U4.13 (PD7(AIN1))
unnamed: C9.2, U4.21 (AREF)
SCL: U4.28 (PC5(ADC5/SCL))
SDA: U4.27 (PC4(ADC4/SDA))
SW_RST: CN3.3, R46.1, U4.1 (PC6(/RESET))
SW_RX: CN3.2, U4.2 (PD0(RXD))
SW_TX: CN3.4, U4.3 (PD1(TXD))
VCC: C3.1, C9.1, CN3.5, IC5.15 (VREF), IC5.16 (VDD), JP7.1, JP8.1, JP9.1, JP10.1, JP11.1, JP12.1, R46.2, U4.7 (VCC), U4.20 (AVCC)

Notes on the sheet:
Simple Wires Module
Programming header

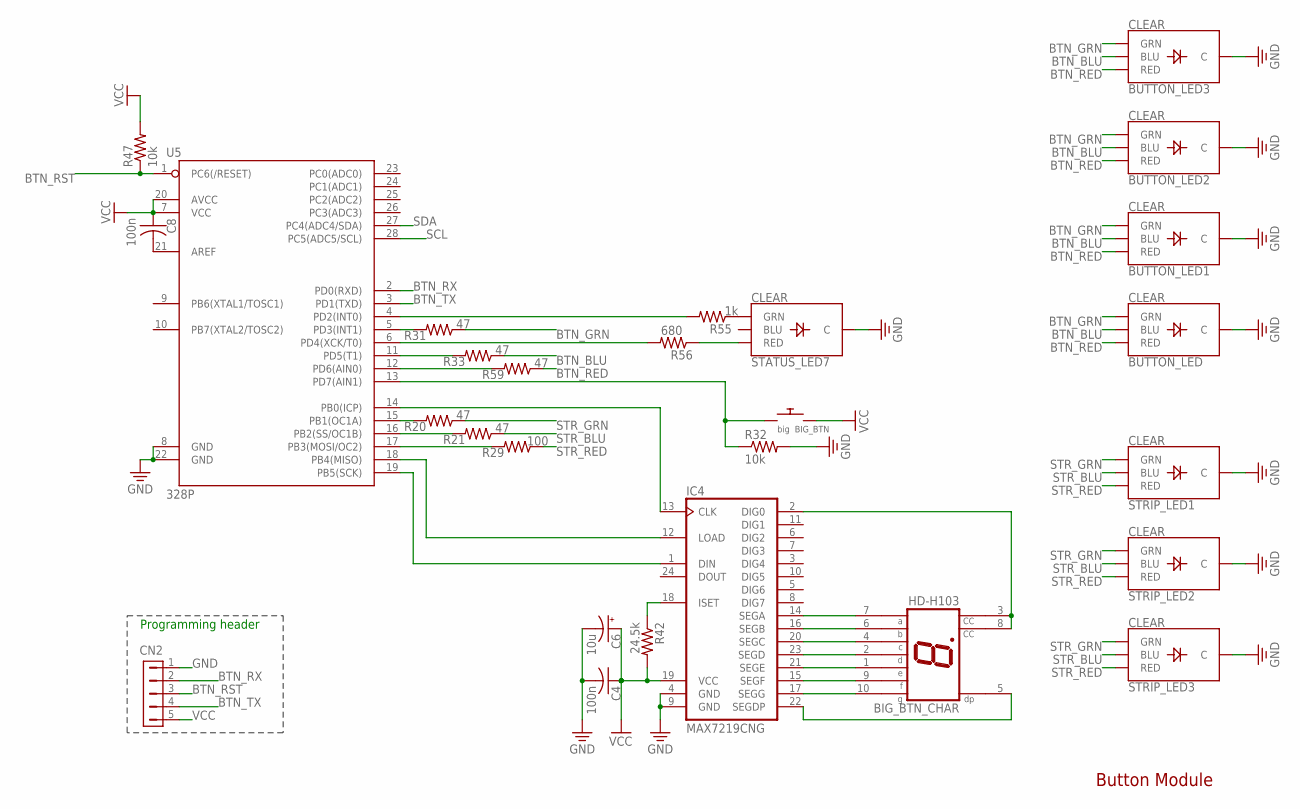
[picture p57: schematic allModules.sch, sheet 6]

Parts:
BIG_BTN: big; TACT_PANA-EVQ
BIG_BTN_CHAR: HD-H103; HDSP-M
BUTTON_LED, BUTTON_LED1, BUTTON_LED2, BUTTON_LED3: CLEAR; LED-RGB-THRU
C4, C8: 100n; C025-024X044
C6: 10u; 085CS_1AR
CN2: HDR-1X5-SIP-100; SIP-100-5V
IC4: MAX7219CNG; DIL24-3
R20, R21, R31, R33, R59: 47; 0805-THM
R29: 100; 0805-THM
R32, R47: 10k; 0309/12
R42: 24.5k; 0309/12
R55: 1k; 0805-THM
R56: 680; 0805-THM
STATUS_LED7: CLEAR; LED-RGB-THRU
STRIP_LED1, STRIP_LED2, STRIP_LED3: CLEAR; LED-RGB-THRU
U5: 328P; DIP28

Connections:
BTN_BLU: BUTTON_LED.4 (BLU), BUTTON_LED1.4 (BLU), BUTTON_LED2.4 (BLU), BUTTON_LED3.4 (BLU), R33.1
BTN_GRN: BUTTON_LED.3 (GRN), BUTTON_LED1.3 (GRN), BUTTON_LED2.3 (GRN), BUTTON_LED3.3 (GRN), R31.1
BTN_RED: BUTTON_LED.1 (RED), BUTTON_LED1.1 (RED), BUTTON_LED2.1 (RED), BUTTON_LED3.1 (RED), R59.1
BTN_RST: CN2.3, R47.1, U5.1 (PC6(/RESET))
BTN_RX: CN2.2, U5.2 (PD0(RXD))
BTN_TX: CN2.4, U5.3 (PD1(TXD))
GND: BUTTON_LED.2 (C), BUTTON_LED1.2 (C), BUTTON_LED2.2 (C), BUTTON_LED3.2 (C), C4.2, C6.-, CN2.1, IC4.4 (GND), IC4.9 (GND), R32.2, STATUS_LED7.2 (C), STRIP_LED1.2 (C), STRIP_LED2.2 (C), STRIP_LED3.2 (C), U5.8 (GND), U5.22 (GND)
unnamed: R20.2, U5.15 (PB1(OC1A))
unnamed: R21.2, U5.16 (PB2(SS/OC1B))
unnamed: R29.2, U5.17 (PB3(MOSI/OC2))
unnamed: R31.2, U5.5 (PD3(INT1))
unnamed: R33.2, U5.11 (PD5(T1))
unnamed: R59.2, U5.12 (PD6(AIN0))
unnamed: R55.2, U5.4 (PD2(INT0))
unnamed: BIG_BTN.P$1, R32.1, U5.13 (PD7(AIN1))
unnamed: BIG_BTN_CHAR.7 (A), IC4.14 (SEGA)
unnamed: R56.2, U5.6 (PD4(XCK/T0))
unnamed: BIG_BTN_CHAR.6 (B), IC4.16 (SEGB)
unnamed: IC4.13 (CLK), U5.14 (PB0(ICP))
unnamed: BIG_BTN_CHAR.4 (C), IC4.20 (SEGC)
unnamed: C8.2, U5.21 (AREF)
unnamed: IC4.18 (ISET), R42.1
unnamed: IC4.1 (DIN), U5.19 (PB5(SCK))
unnamed: IC4.12 (LOAD), U5.18 (PB4(MISO))
unnamed: BIG_BTN_CHAR.2 (D), IC4.23 (SEGD)
unnamed: BIG_BTN_CHAR.1 (E), IC4.21 (SEGE)
unnamed: BIG_BTN_CHAR.9 (F), IC4.15 (SEGF)
unnamed: BIG_BTN_CHAR.10 (G), IC4.17 (SEGG)
unnamed: BIG_BTN_CHAR.5 (DP), IC4.22 (SEGDP)
unnamed: BIG_BTN_CHAR.3 (CC), BIG_BTN_CHAR.8 (CC), IC4.2 (DIG0)
unnamed: R55.1, STATUS_LED7.3 (GRN)
unnamed: R56.1, STATUS_LED7.1 (RED)
SCL: U5.28 (PC5(ADC5/SCL))
SDA: U5.27 (PC4(ADC4/SDA))
STR_BLU: R21.1, STRIP_LED1.4 (BLU), STRIP_LED2.4 (BLU), STRIP_LED3.4 (BLU)
STR_GRN: R20.1, STRIP_LED1.3 (GRN), STRIP_LED2.3 (GRN), STRIP_LED3.3 (GRN)
STR_RED: R29.1, STRIP_LED1.1 (RED), STRIP_LED2.1 (RED), STRIP_LED3.1 (RED)
VCC: BIG_BTN.P$2, C4.1, C6.+, C8.1, CN2.5, IC4.19 (VCC), R42.2, R47.2, U5.7 (VCC), U5.20 (AVCC)

Notes on the sheet:
Button Module
Programming header

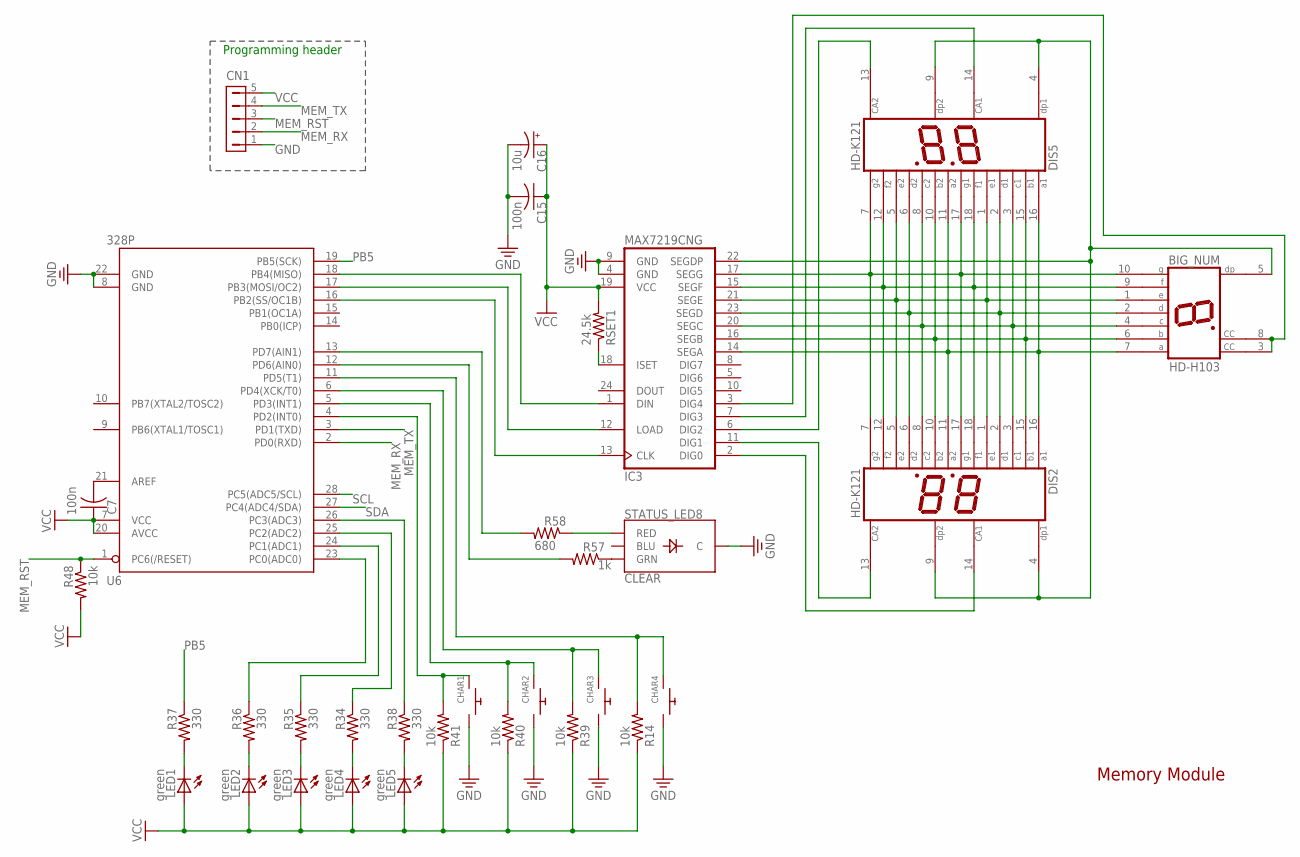
[picture p58: schematic allModules.sch, sheet 7]

Parts:
BIG_NUM: HD-H103; HDSP-M
C7, C15: 100n; C025-024X044
C16: 10u; 085CS_1AR
CHAR1, CHAR2, CHAR3, CHAR4: SWITCH_PUSHBUTTONEVQ-PE; TACT_PANA-EVQ
CN1: HDR-1X5-SIP-100; SIP-100-5V
DIS2, DIS5: HD-K121; HDSP-R
IC3: MAX7219CNG; DIL24-3
LED1, LED2, LED3, LED4, LED5: green; LED5MM
R14, R39, R40, R41, R48: 10k; 0309/12
R34, R35, R36, R37, R38: 330; 0309/12
R57: 1k; 0805-THM
R58: 680; 0805-THM
RSET1: 24.5k; 0204/7
STATUS_LED8: CLEAR; LED-RGB-THRU
U6: 328P; DIP28

Connections:
GND: C15.2, C16.-, CHAR1.P$1, CHAR2.P$1, CHAR3.P$1, CHAR4.P$1, CN1.1, IC3.4 (GND), IC3.9 (GND), STATUS_LED8.2 (C), U6.8 (GND), U6.22 (GND)
MEM_RST: CN1.3, R48.1, U6.1 (PC6(/RESET))
MEM_RX: CN1.2, U6.2 (PD0(RXD))
MEM_TX: CN1.4, U6.3 (PD1(TXD))
unnamed: BIG_NUM.7 (A), DIS2.11 (A2), DIS2.16 (A1), DIS5.11 (A2), DIS5.16 (A1), IC3.14 (SEGA)
unnamed: BIG_NUM.6 (B), DIS2.10 (B2), DIS2.15 (B1), DIS5.10 (B2), DIS5.15 (B1), IC3.16 (SEGB)
unnamed: BIG_NUM.4 (C), DIS2.3 (C1), DIS2.8 (C2), DIS5.3 (C1), DIS5.8 (C2), IC3.20 (SEGC)
unnamed: BIG_NUM.2 (D), DIS2.2 (D1), DIS2.6 (D2), DIS5.2 (D1), DIS5.6 (D2), IC3.23 (SEGD)
unnamed: BIG_NUM.1 (E), DIS2.1 (E1), DIS2.5 (E2), DIS5.1 (E1), DIS5.5 (E2), IC3.21 (SEGE)
unnamed: BIG_NUM.9 (F), DIS2.12 (F2), DIS2.18 (F1), DIS5.12 (F2), DIS5.18 (F1), IC3.15 (SEGF)
unnamed: BIG_NUM.10 (G), DIS2.7 (G2), DIS2.17 (G1), DIS5.7 (G2), DIS5.17 (G1), IC3.17 (SEGG)
unnamed: BIG_NUM.5 (DP), DIS2.4 (DP1), DIS2.9 (DP2), DIS5.4 (DP1), DIS5.9 (DP2), IC3.22 (SEGDP)
unnamed: R57.2, U6.12 (PD6(AIN0))
unnamed: R58.2, U6.13 (PD7(AIN1))
unnamed: DIS5.14 (CA1), IC3.7 (DIG3)
unnamed: DIS5.13 (CA2), IC3.6 (DIG2)
unnamed: DIS2.13 (CA2), IC3.11 (DIG1)
unnamed: DIS2.14 (CA1), IC3.2 (DIG0)
unnamed: LED1.K (C), R37.2
unnamed: LED2.K (C), R36.2
unnamed: C7.2, U6.21 (AREF)
unnamed: IC3.18 (ISET), RSET1.1
unnamed: LED3.K (C), R35.2
unnamed: LED4.K (C), R34.2
unnamed: LED5.K (C), R38.2
unnamed: R35.1, R36.1, R38.1, U6.23 (PC0(ADC0)), U6.24 (PC1(ADC1)), U6.26 (PC3(ADC3))
unnamed: BIG_NUM.3 (CC), BIG_NUM.8 (CC), IC3.3 (DIG4)
unnamed: CHAR1.P$2, R41.2, U6.4 (PD2(INT0))
unnamed: IC3.13 (CLK), U6.16 (PB2(SS/OC1B))
unnamed: CHAR3.P$2, R39.2, U6.6 (PD4(XCK/T0))
unnamed: CHAR4.P$2, R14.2, U6.11 (PD5(T1))
unnamed: R34.1, U6.25 (PC2(ADC2))
unnamed: IC3.12 (LOAD), U6.17 (PB3(MOSI/OC2))
unnamed: CHAR2.P$2, R40.2, U6.5 (PD3(INT1))
unnamed: IC3.1 (DIN), U6.18 (PB4(MISO))
unnamed: R57.1, STATUS_LED8.3 (GRN)
unnamed: R58.1, STATUS_LED8.1 (RED)
PB5: R37.1, U6.19 (PB5(SCK))
SCL: U6.28 (PC5(ADC5/SCL))
SDA: U6.27 (PC4(ADC4/SDA))
VCC: C7.1, C15.1, C16.+, CN1.5, IC3.19 (VCC), LED1.A, LED2.A, LED3.A, LED4.A, LED5.A, R14.1, R39.1, R40.1, R41.1, R48.2, RSET1.2, U6.7 (VCC), U6.20 (AVCC)

Notes on the sheet:
Memory Module
Programming header
